CryptoIceMLH/ESP-Miner-LAN/main/global_state.h

#ifndef GLOBAL_STATE_H_
#define GLOBAL_STATE_H_

#include <stdbool.h>
#include <stdint.h>
#include "asic_task.h"
#include "common.h"
#include "power_management_task.h"
#include "statistics_task.h"
#include "serial.h"
#include "stratum_api.h"
#include "work_queue.h"
#include "device_config.h"
#include "display.h"

#define STRATUM_USER CONFIG_STRATUM_USER
#define FALLBACK_STRATUM_USER CONFIG_FALLBACK_STRATUM_USER

#define HISTORY_LENGTH 100
#define DIFF_STRING_SIZE 10

typedef enum {
    NETWORK_MODE_WIFI = 0,
    NETWORK_MODE_ETHERNET = 1
} network_mode_t;

typedef struct {
    char message[64];
    uint32_t count;
} RejectedReasonStat;

typedef struct
{
    double duration_start;
    int historical_hashrate_rolling_index;
    double historical_hashrate_time_stamps[HISTORY_LENGTH];
    double historical_hashrate[HISTORY_LENGTH];
    int historical_hashrate_init;
    double current_hashrate;
    int64_t start_time;
    uint64_t shares_accepted;
    uint64_t shares_rejected;
    uint64_t work_received;
    RejectedReasonStat rejected_reason_stats[10];
    int rejected_reason_stats_count;
    int screen_page;
    uint64_t best_nonce_diff;
    char best_diff_string[DIFF_STRING_SIZE];
    uint64_t best_session_nonce_diff;
    char best_session_diff_string[DIFF_STRING_SIZE];
    bool block_found;
    char ssid[32];
    char wifi_status[256];
    char ip_addr_str[16]; // IP4ADDR_STRLEN_MAX
    char ipv6_addr_str[40]; // IPv6 address string
    char ap_ssid[32];
    bool ap_enabled;
    bool is_connected;
    char * pool_url;
    char * fallback_pool_url;
    uint16_t pool_port;
    uint16_t fallback_pool_port;
    char * pool_user;
    char * fallback_pool_user;
    char * pool_pass;
    char * fallback_pool_pass;
    uint16_t pool_difficulty;
    uint16_t fallback_pool_difficulty;
    bool pool_extranonce_subscribe;
    bool fallback_pool_extranonce_subscribe;
    double response_time;
    bool is_using_fallback;
    uint16_t overheat_mode;
    uint16_t power_fault;
    uint32_t lastClockSync;
    bool is_screen_active;
    bool is_firmware_update;
    char firmware_update_filename[20];
    char firmware_update_status[20];
    char * asic_status;
} SystemModule;

typedef struct
{
    network_mode_t network_mode;
    bool eth_available;      // W5500 SPI hardware detected
    bool eth_link_up;        // Physical cable connected (PHY link)
    bool eth_connected;      // Has IP address (DHCP or static)
    char eth_ip_addr_str[16];
    char eth_mac_str[18];
    bool eth_use_dhcp;
    char eth_static_ip[16];
    char eth_gateway[16];
    char eth_subnet[16];
    char eth_dns[16];
} EthernetModule;

typedef struct
{
    bool is_active;
    bool is_finished;
    char *message;
    char *result;
    char *finished;
} SelfTestModule;

typedef struct
{
    work_queue stratum_queue;
    work_queue ASIC_jobs_queue;

    SystemModule SYSTEM_MODULE;
    EthernetModule ETHERNET_MODULE;
    DeviceConfig DEVICE_CONFIG;
    DisplayConfig DISPLAY_CONFIG;
    AsicTaskModule ASIC_TASK_MODULE;
    PowerManagementModule POWER_MANAGEMENT_MODULE;
    SelfTestModule SELF_TEST_MODULE;
    StatisticsModule STATISTICS_MODULE;

    char * extranonce_str;
    int extranonce_2_len;
    int abandon_work;

    uint8_t * valid_jobs;
    pthread_mutex_t valid_jobs_lock;

    uint32_t pool_difficulty;
    bool new_set_mining_difficulty_msg;
    uint32_t version_mask;
    bool new_stratum_version_rolling_msg;

    int sock;

    // A message ID that must be unique per request that expects a response.
    // For requests not expecting a response (called notifications), this is null.
    int send_uid;

    bool ASIC_initalized;
    bool psram_is_available;

    int block_height;
    char * scriptsig;
    char network_diff_string[DIFF_STRING_SIZE];
} GlobalState;

#endif /* GLOBAL_STATE_H_ */
