CryptoIceMLH/ESP-Miner-LAN/components/ethernet_w5500/ethernet_w5500.c

/**
 * @file ethernet_w5500.c
 * @brief W5500 Ethernet driver using ESP-IDF native esp_eth component
 * Professional implementation matching ESP-IDF patterns
 */

#include "ethernet_w5500.h"
#include "esp_log.h"
#include "esp_mac.h"
#include "esp_eth.h"
#include "esp_eth_mac_spi.h"
#include "esp_eth_phy.h"
#include "esp_netif.h"
#include "esp_event.h"
#include "driver/spi_master.h"
#include "driver/gpio.h"
#include "freertos/FreeRTOS.h"
#include "freertos/task.h"
#include <string.h>

static const char *TAG = "w5500_eth";

// SPI configuration from Kconfig
#define W5500_SPI_HOST      SPI2_HOST
#define W5500_SPI_MOSI      CONFIG_W5500_SPI_MOSI
#define W5500_SPI_MISO      CONFIG_W5500_SPI_MISO
#define W5500_SPI_SCLK      CONFIG_W5500_SPI_SCLK
#define W5500_SPI_CS        CONFIG_W5500_SPI_CS
#define W5500_SPI_CLOCK_MHZ CONFIG_W5500_SPI_CLOCK_MHZ
#define W5500_INT_GPIO      CONFIG_W5500_INT_GPIO

// Module state
static esp_eth_handle_t eth_handle = NULL;
static esp_netif_t *eth_netif = NULL;
static uint8_t eth_mac_addr[6];
static bool eth_started = false;
static bool eth_link_up = false;
static bool eth_got_ip = false;

/**
 * @brief Event handler for Ethernet events
 */
static void eth_event_handler(void *arg, esp_event_base_t event_base,
                              int32_t event_id, void *event_data) {
    if (event_base == ETH_EVENT) {
        switch (event_id) {
            case ETHERNET_EVENT_CONNECTED:
                ESP_LOGI(TAG, "Ethernet link UP");
                eth_link_up = true;
                break;
            case ETHERNET_EVENT_DISCONNECTED:
                ESP_LOGW(TAG, "Ethernet link DOWN");
                eth_link_up = false;
                eth_got_ip = false;
                break;
            case ETHERNET_EVENT_START:
                ESP_LOGI(TAG, "Ethernet started");
                eth_started = true;
                break;
            case ETHERNET_EVENT_STOP:
                ESP_LOGI(TAG, "Ethernet stopped");
                eth_started = false;
                eth_link_up = false;
                eth_got_ip = false;
                break;
            default:
                break;
        }
    }
}

/**
 * @brief Event handler for IP events
 */
static void ip_event_handler(void *arg, esp_event_base_t event_base,
                             int32_t event_id, void *event_data) {
    if (event_base == IP_EVENT && event_id == IP_EVENT_ETH_GOT_IP) {
        ip_event_got_ip_t *event = (ip_event_got_ip_t *)event_data;
        const esp_netif_ip_info_t *ip_info = &event->ip_info;

        ESP_LOGI(TAG, "Ethernet Got IP:");
        ESP_LOGI(TAG, "  IP: " IPSTR, IP2STR(&ip_info->ip));
        ESP_LOGI(TAG, "  Gateway: " IPSTR, IP2STR(&ip_info->gw));
        ESP_LOGI(TAG, "  Netmask: " IPSTR, IP2STR(&ip_info->netmask));

        eth_got_ip = true;
    }
}

/**
 * @brief Generate unique MAC address from ESP32 chip ID
 */
static void generate_mac_address(uint8_t *mac) {
    uint8_t base_mac[6];
    esp_err_t err = esp_efuse_mac_get_default(base_mac);
    if (err != ESP_OK) {
        ESP_LOGW(TAG, "Failed to get base MAC, using fallback");
        mac[0] = 0x02;
        mac[1] = 0x00;
        mac[2] = 0x00;
        mac[3] = 0x00;
        mac[4] = 0x00;
        mac[5] = 0x01;
        return;
    }

    // Derive Ethernet MAC from WiFi MAC
    mac[0] = base_mac[0] | 0x02;  // Locally administered
    mac[1] = base_mac[1];
    mac[2] = base_mac[2];
    mac[3] = base_mac[3];
    mac[4] = base_mac[4];
    mac[5] = base_mac[5] ^ 0x01;  // Differentiate from WiFi
}

esp_err_t ethernet_w5500_init(void) {
    if (eth_handle != NULL) {
        ESP_LOGW(TAG, "Ethernet already initialized");
        return ESP_OK;
    }

    ESP_LOGI(TAG, "Initializing W5500 Ethernet (ESP-IDF native driver)");
    ESP_LOGI(TAG, "SPI Pins - MOSI:%d MISO:%d SCLK:%d CS:%d",
             W5500_SPI_MOSI, W5500_SPI_MISO, W5500_SPI_SCLK, W5500_SPI_CS);

    // Initialize SPI bus
    spi_bus_config_t buscfg = {
        .miso_io_num = W5500_SPI_MISO,
        .mosi_io_num = W5500_SPI_MOSI,
        .sclk_io_num = W5500_SPI_SCLK,
        .quadwp_io_num = -1,
        .quadhd_io_num = -1,
    };

    esp_err_t ret = spi_bus_initialize(W5500_SPI_HOST, &buscfg, SPI_DMA_CH_AUTO);
    if (ret == ESP_ERR_INVALID_STATE) {
        ESP_LOGI(TAG, "SPI bus already initialized");
    } else if (ret != ESP_OK) {
        ESP_LOGE(TAG, "SPI bus init failed: %s", esp_err_to_name(ret));
        return ret;
    }

    // Wait for W5500 chip to stabilize after power-on
    // W5500 datasheet requires ~50ms for power stabilization + PLL lock
    ESP_LOGI(TAG, "Waiting 100ms for W5500 chip stabilization...");
    vTaskDelay(pdMS_TO_TICKS(100));

    // Generate MAC address
    generate_mac_address(eth_mac_addr);
    ESP_LOGI(TAG, "MAC: %02X:%02X:%02X:%02X:%02X:%02X",
             eth_mac_addr[0], eth_mac_addr[1], eth_mac_addr[2],
             eth_mac_addr[3], eth_mac_addr[4], eth_mac_addr[5]);

    // Configure SPI interface for W5500
    spi_device_interface_config_t devcfg = {
        .command_bits = 16,
        .address_bits = 8,
        .mode = 0,
        .clock_speed_hz = W5500_SPI_CLOCK_MHZ * 1000 * 1000,
        .queue_size = 20,
        .spics_io_num = W5500_SPI_CS,
    };

    // Create W5500-specific configuration
    eth_w5500_config_t w5500_config = ETH_W5500_DEFAULT_CONFIG(W5500_SPI_HOST, &devcfg);
    w5500_config.int_gpio_num = W5500_INT_GPIO;

    // If no interrupt GPIO configured, use polling mode instead
    // ESP-IDF requires exactly one mode: interrupt XOR polling
    if (W5500_INT_GPIO < 0) {
        w5500_config.poll_period_ms = 1;  // Poll every 1ms
        ESP_LOGI(TAG, "Using polling mode (no interrupt GPIO configured)");
    } else {
        ESP_LOGI(TAG, "Using interrupt mode on GPIO %d", W5500_INT_GPIO);
    }

    // Create MAC configuration (no SMI fields for SPI Ethernet)
    eth_mac_config_t mac_config = ETH_MAC_DEFAULT_CONFIG();

    // Create PHY configuration
    eth_phy_config_t phy_config = ETH_PHY_DEFAULT_CONFIG();
    phy_config.phy_addr = 1;
    phy_config.reset_gpio_num = -1;

    // Create MAC and PHY instances
    esp_eth_mac_t *mac = esp_eth_mac_new_w5500(&w5500_config, &mac_config);
    esp_eth_phy_t *phy = esp_eth_phy_new_w5500(&phy_config);

    // Install Ethernet driver
    esp_eth_config_t eth_config = ETH_DEFAULT_CONFIG(mac, phy);
    ret = esp_eth_driver_install(&eth_config, &eth_handle);
    if (ret != ESP_OK) {
        ESP_LOGE(TAG, "Ethernet driver install failed: %s", esp_err_to_name(ret));
        return ret;
    }

    // Set MAC address
    ret = esp_eth_ioctl(eth_handle, ETH_CMD_S_MAC_ADDR, eth_mac_addr);
    if (ret != ESP_OK) {
        ESP_LOGE(TAG, "Failed to set MAC address: %s", esp_err_to_name(ret));
        esp_eth_driver_uninstall(eth_handle);
        eth_handle = NULL;
        return ret;
    }

    // Create network interface
    esp_netif_config_t netif_config = ESP_NETIF_DEFAULT_ETH();
    eth_netif = esp_netif_new(&netif_config);

    // Attach Ethernet driver to network interface
    ret = esp_netif_attach(eth_netif, esp_eth_new_netif_glue(eth_handle));
    if (ret != ESP_OK) {
        ESP_LOGE(TAG, "Failed to attach netif: %s", esp_err_to_name(ret));
        esp_eth_driver_uninstall(eth_handle);
        eth_handle = NULL;
        return ret;
    }

    // Register event handlers
    ret = esp_event_handler_register(ETH_EVENT, ESP_EVENT_ANY_ID, &eth_event_handler, NULL);
    if (ret != ESP_OK) {
        ESP_LOGE(TAG, "Failed to register ETH event handler: %s", esp_err_to_name(ret));
        return ret;
    }

    ret = esp_event_handler_register(IP_EVENT, IP_EVENT_ETH_GOT_IP, &ip_event_handler, NULL);
    if (ret != ESP_OK) {
        ESP_LOGE(TAG, "Failed to register IP event handler: %s", esp_err_to_name(ret));
        return ret;
    }

    // Start Ethernet driver
    ret = esp_eth_start(eth_handle);
    if (ret != ESP_OK) {
        ESP_LOGE(TAG, "Ethernet start failed: %s", esp_err_to_name(ret));
        return ret;
    }

    ESP_LOGI(TAG, "W5500 initialization complete");
    return ESP_OK;
}

bool ethernet_w5500_is_available(void) {
    return eth_handle != NULL;
}

bool ethernet_w5500_is_connected(void) {
    return eth_link_up && eth_got_ip;
}

esp_err_t ethernet_w5500_get_ip(char *ip_str, size_t len) {
    if (ip_str == NULL || eth_netif == NULL) {
        return ESP_ERR_INVALID_ARG;
    }

    esp_netif_ip_info_t ip_info;
    esp_err_t ret = esp_netif_get_ip_info(eth_netif, &ip_info);
    if (ret != ESP_OK) {
        return ret;
    }

    snprintf(ip_str, len, IPSTR, IP2STR(&ip_info.ip));
    return ESP_OK;
}

esp_err_t ethernet_w5500_get_mac(char *mac_str, size_t len) {
    if (mac_str == NULL) {
        return ESP_ERR_INVALID_ARG;
    }

    snprintf(mac_str, len, "%02X:%02X:%02X:%02X:%02X:%02X",
             eth_mac_addr[0], eth_mac_addr[1], eth_mac_addr[2],
             eth_mac_addr[3], eth_mac_addr[4], eth_mac_addr[5]);

    return ESP_OK;
}

void ethernet_w5500_check_link(void) {
    // Not needed - events handle this automatically
}

bool ethernet_w5500_get_link_status(void) {
    return eth_link_up;
}

esp_err_t ethernet_w5500_stop(void) {
    if (eth_handle == NULL) {
        return ESP_OK;
    }

    ESP_LOGI(TAG, "Stopping Ethernet...");

    esp_event_handler_unregister(ETH_EVENT, ESP_EVENT_ANY_ID, &eth_event_handler);
    esp_event_handler_unregister(IP_EVENT, IP_EVENT_ETH_GOT_IP, &ip_event_handler);

    esp_eth_stop(eth_handle);
    esp_eth_driver_uninstall(eth_handle);

    if (eth_netif) {
        esp_netif_destroy(eth_netif);
        eth_netif = NULL;
    }

    spi_bus_free(W5500_SPI_HOST);

    eth_handle = NULL;
    eth_started = false;
    eth_link_up = false;
    eth_got_ip = false;

    ESP_LOGI(TAG, "Ethernet stopped");
    return ESP_OK;
}

esp_err_t ethernet_w5500_restart(void) {
    ESP_LOGI(TAG, "Restarting Ethernet...");
    ethernet_w5500_stop();
    vTaskDelay(pdMS_TO_TICKS(1000));
    return ethernet_w5500_init();
}
